takshcpatel/automatic-turret/CAD Files/Tilt/Gun/GearTrain - Spur 1.25M 10T.step

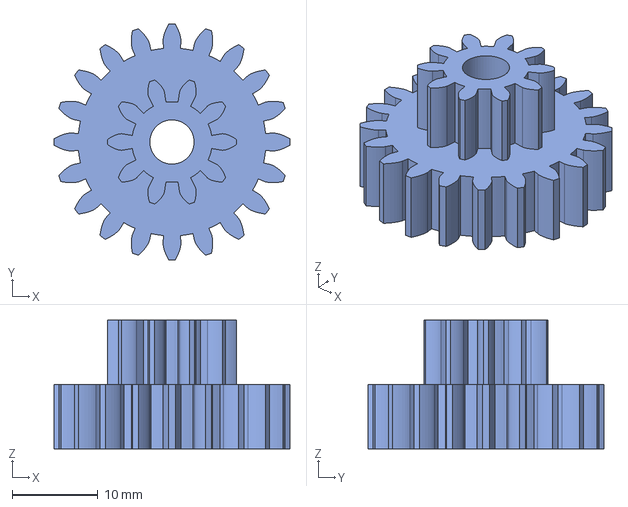
[picture p20: CAD file, 2026-02-05]
CAD Files/Tilt/Gun/GearTrain - Spur 1.25M 10T.step
27.5 x 27.5 x 15.0 mm
