takshcpatel/automatic-turret/CAD Files/Tilt/Gun/Face plate - Face Plate.step

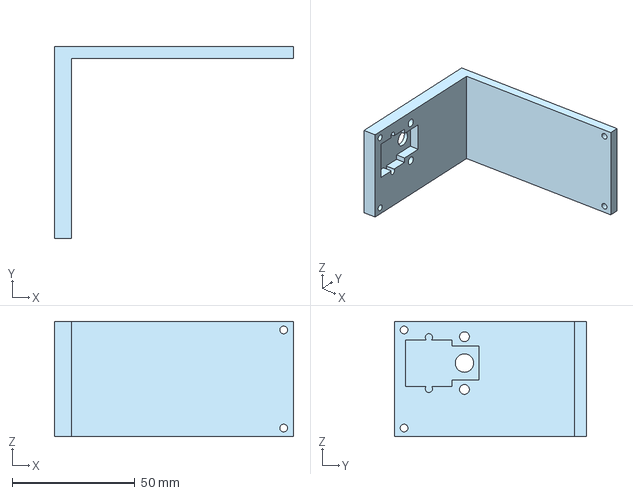
[picture p21: CAD file, 2026-02-05]
CAD Files/Tilt/Gun/Face plate - Face Plate.step
97.5 x 78.5 x 47.0 mm
