takshcpatel/automatic-turret/CAD Files/Tilt/Gun/GearTrain - Spur 1.25M 10T (2).step

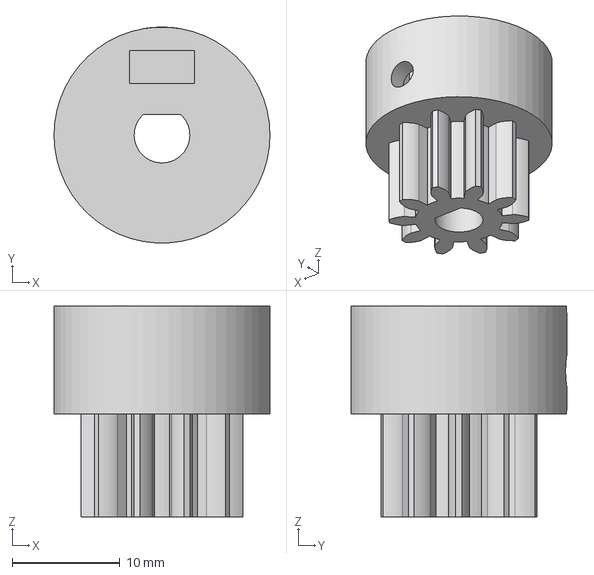
[picture p22: CAD file, 2026-02-05, an earlier design]
CAD Files/Tilt/Gun/GearTrain - Spur 1.25M 10T (2).step
20.0 x 20.0 x 19.5 mm
